JTOLEDOJ/Tabuleiro-de-Xadrez-Interativo/Montagem/Peao (Preto).SLDPRT

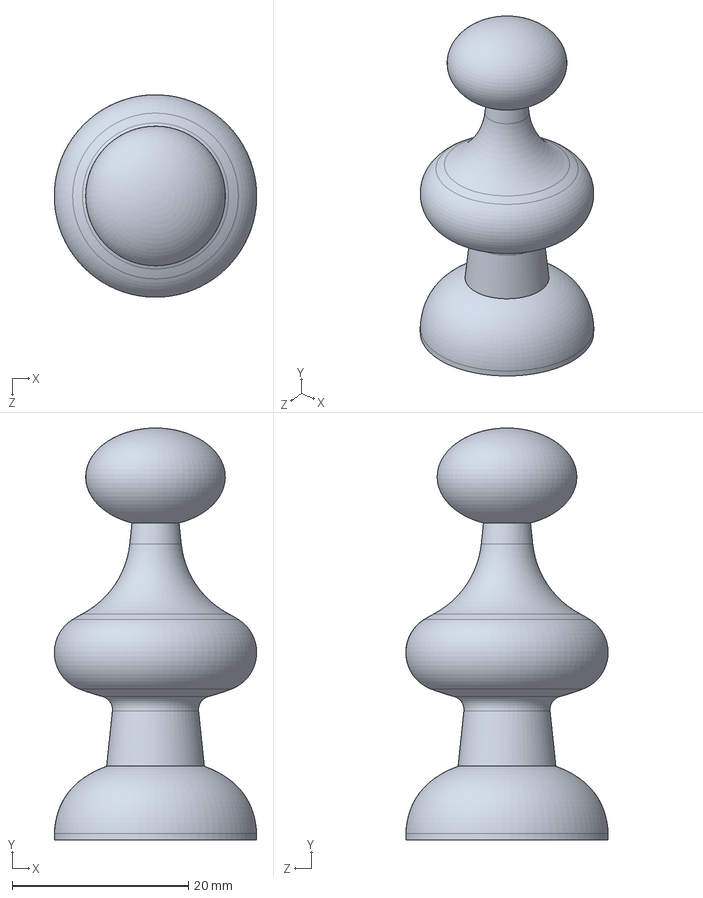
[picture p50: CAD file, 2018-11-23]
Montagem/Peao (Preto).SLDPRT
23.0 x 46.8 x 23.0 mm
