JTOLEDOJ/Tabuleiro-de-Xadrez-Interativo/Montagem/Porca.SLDPRT

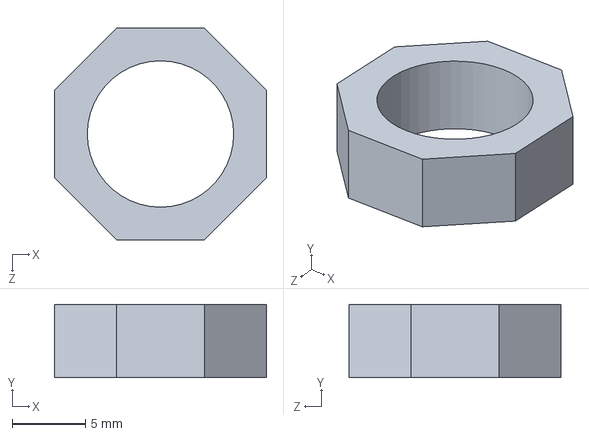
[picture p51: CAD file, 2018-11-23]
Montagem/Porca.SLDPRT
14.5 x 5.00 x 14.5 mm
