JTOLEDOJ/Tabuleiro-de-Xadrez-Interativo/Montagem/Superficie1.SLDPRT

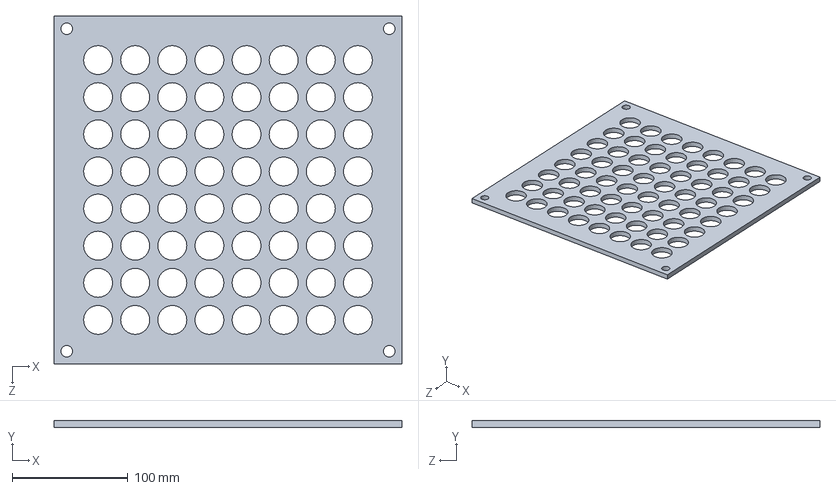
[picture p52: CAD file, 2018-11-23]
Montagem/Superficie1.SLDPRT
300.0 x 6.00 x 300.0 mm
