JTOLEDOJ/Tabuleiro-de-Xadrez-Interativo/Montagem/Arruela.SLDPRT

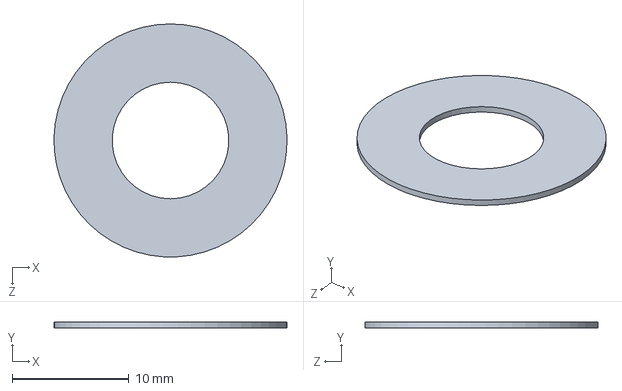
[picture p53: CAD file, 2018-11-23]
Montagem/Arruela.SLDPRT
20.0 x 0.5 x 20.0 mm
