JTOLEDOJ/Tabuleiro-de-Xadrez-Interativo/Montagem/Rei (Preto).SLDPRT

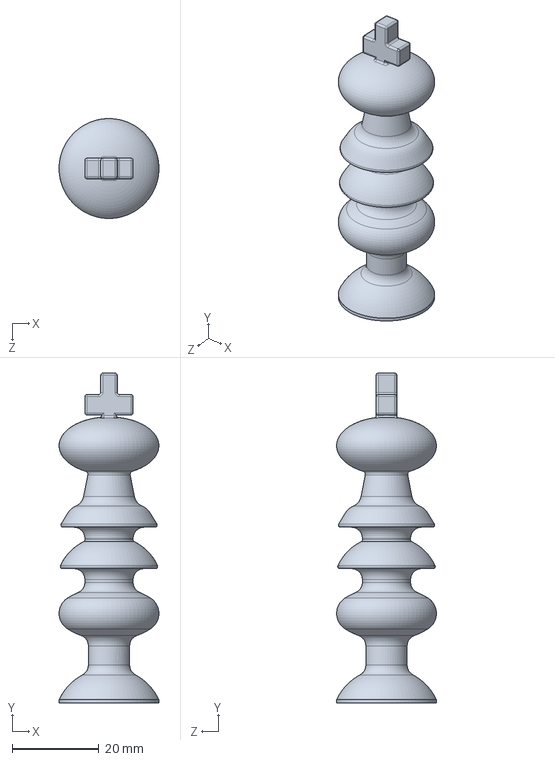
[picture p54: CAD file, 2018-11-23]
Montagem/Rei (Preto).SLDPRT
23.0 x 75.9 x 23.0 mm
