JTOLEDOJ/Tabuleiro-de-Xadrez-Interativo/Montagem/Torre (Preto).SLDPRT

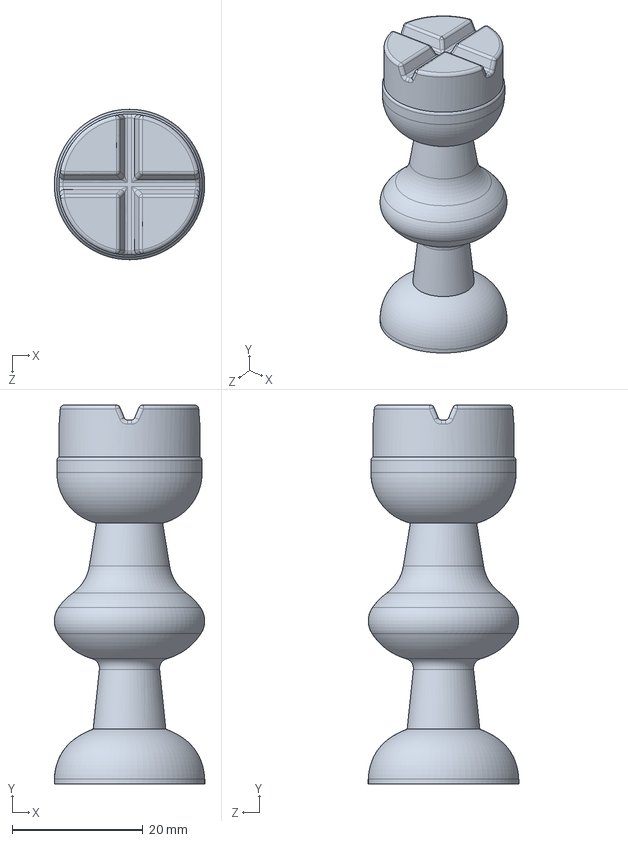
[picture p55: CAD file, 2018-11-23]
Montagem/Torre (Preto).SLDPRT
23.0 x 57.9 x 23.0 mm
