JTOLEDOJ/Tabuleiro-de-Xadrez-Interativo/Montagem/LED.SLDPRT

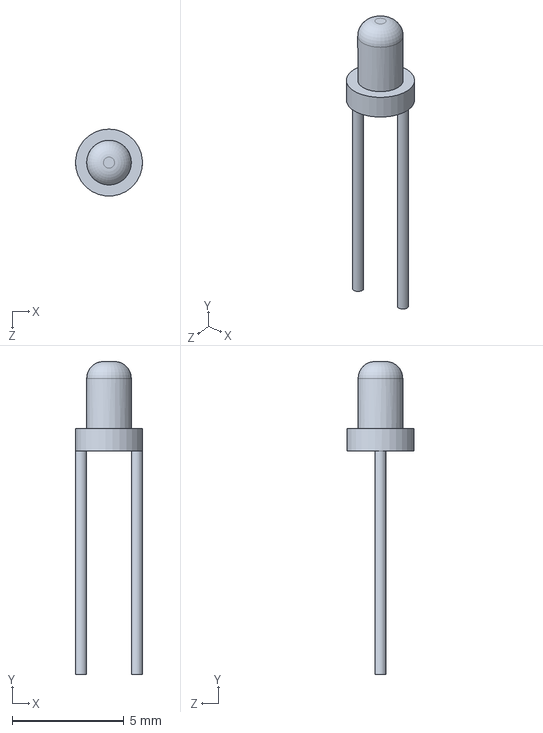
[picture p56: CAD file, 2018-11-23]
Montagem/LED.SLDPRT
3.00 x 14.0 x 2.99 mm
